Singhapur/HBot_miniBot/robot_tfg_pkg/robot_tfg_pkg/camera_publish.py

import cv2
import rclpy
import numpy as np
from rclpy.node import Node
from sensor_msgs.msg import CompressedImage

class CameraPublisher(Node):
    def __init__(self):
        super().__init__('camera_publisher_node')
        
        # 1. Declare the camera params
        self.cameraId = 0 # Id or Number of the camera
        self.camera = cv2.VideoCapture(self.cameraId)
        # Check if the camera is connected correctly 
        ret, frame = self.camera.read()
        while not ret:
            try:
                self.camera = cv2.VideoCapture(self.cameraId)
                ret, frame = self.camera.read()
            except Exception as e:
                self.get_logger().error(f'Camera not detected')
        
        # 2. Publishers: Send results to the rest of the robot of compressed image
        self.publisher_img = self.create_publisher(CompressedImage, '/image_compressed_raw', 15)
        
        # Communication period
        self.periodCommunication = 0.05
        
        # Very fast read timer to prevent losing bytes
        self.timer = self.create_timer(self.periodCommunication, self.timer_callbackFunction)
        
    def timer_callbackFunction(self):
        ret, frame = self.camera.read()
        # if the camera is on, we go on, else return nothing
        if not ret:
            self.get_logger().warning("Failed to capture image")
            return
        target_width = 256
        target_height = 256
        frame = cv2.resize(frame, (target_width, target_height))
        
        encode_param = [int(cv2.IMWRITE_JPEG_QUALITY), 50]
        result, encimg = cv2.imencode('.jpg', frame, encode_param)

        if result:
            msg = CompressedImage()
            msg.header.stamp = self.get_clock().now().to_msg()
            msg.format = "jpeg"
            msg.data = np.array(encimg).tobytes()
            self.publisher_img.publish(msg)
        else:
            self.get_logger().warning("Failed to capture image")

def main(args=None):
    rclpy.init(args=args)
    node = CameraPublisher()
    rclpy.spin(node)
    node.destroy_node()
    rclpy.shutdown()

if __name__ == '__main__':
    main()
